JPeaceK/RepliCube/Images/1.jpg

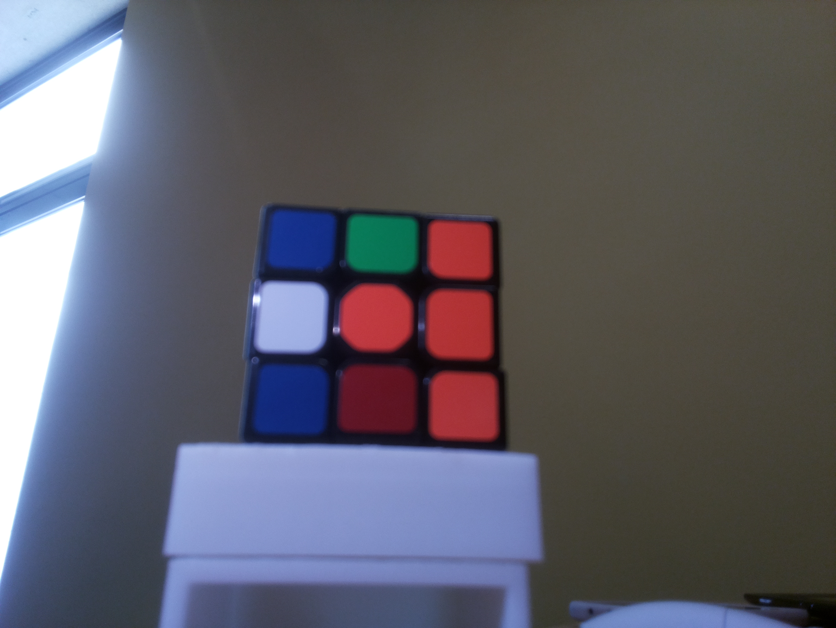
Images/1.jpg
