JPeaceK/RepliCube/Images/3.jpg

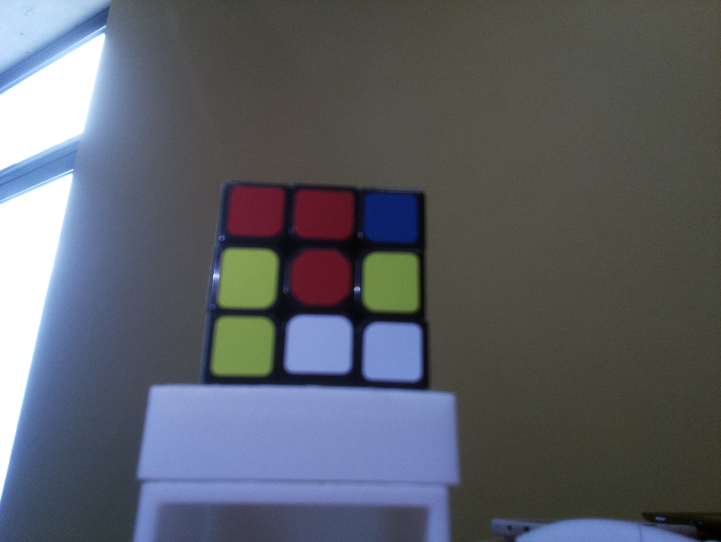
Images/3.jpg
