JPeaceK/RepliCube/Images/4.jpg

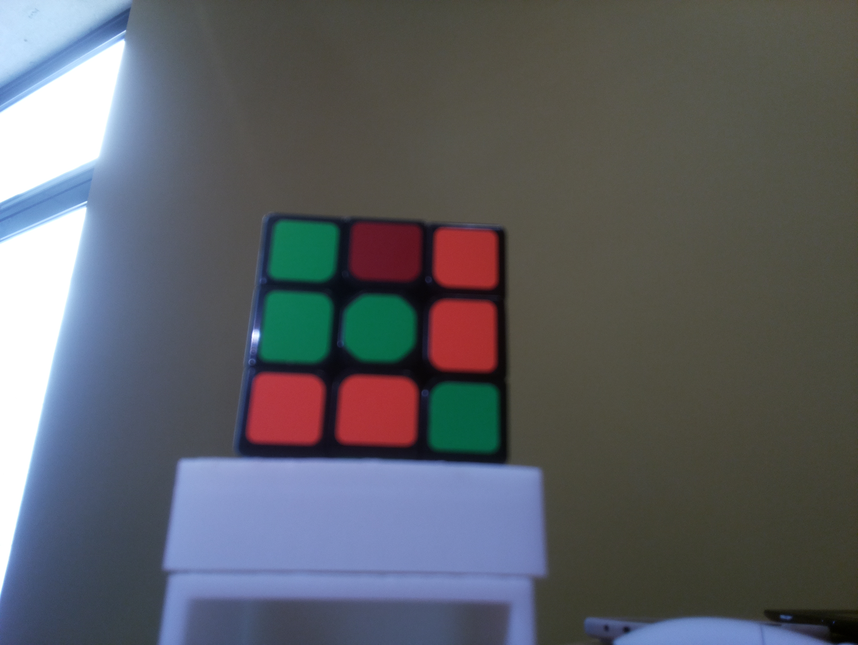
Images/4.jpg
