JPeaceK/RepliCube/Images/6.jpg

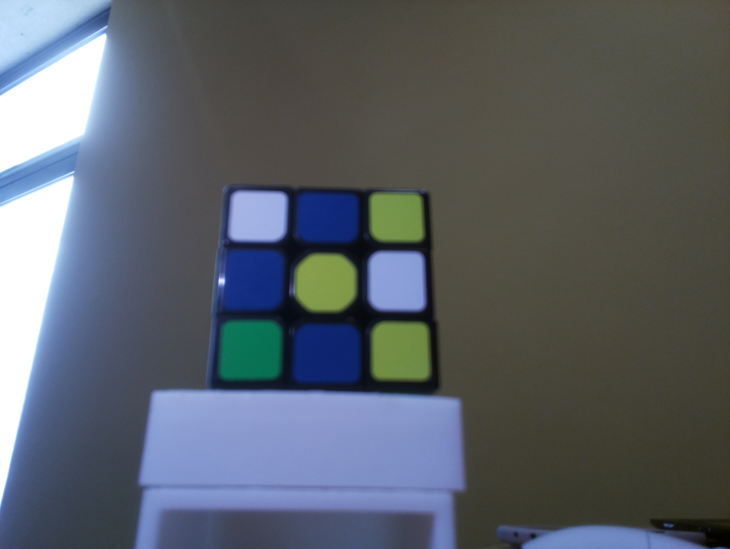
Images/6.jpg
